venko9669-crypto/table/chain_link.png

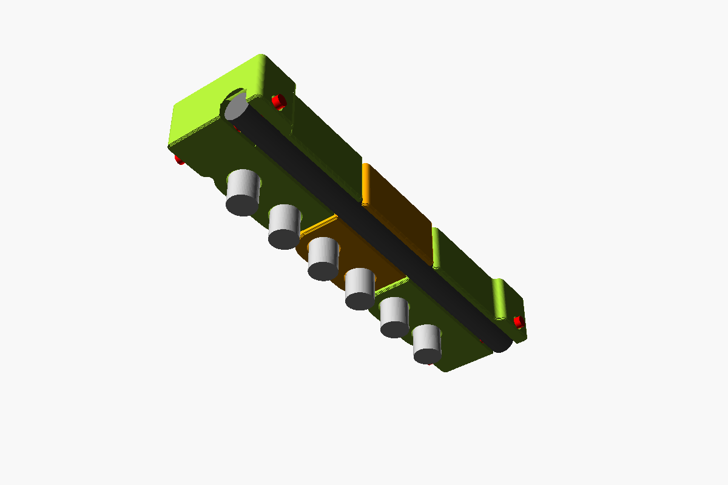
chain_link.png
