venko9669-crypto/table/chain_link_open.png

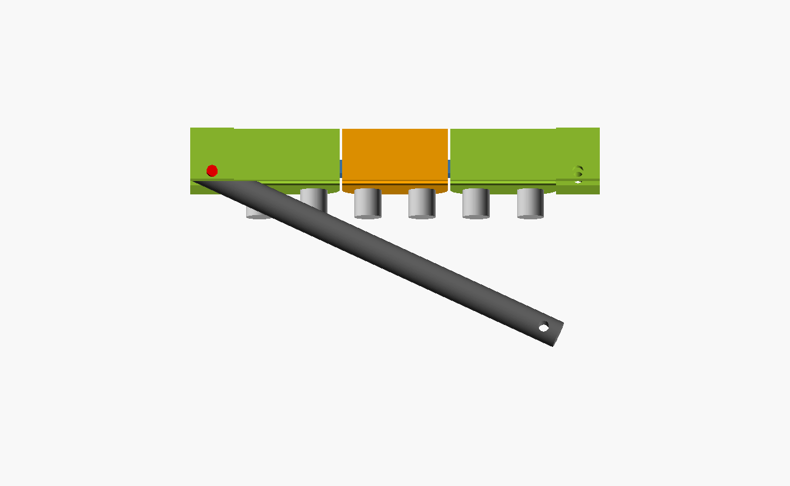
chain_link_open.png
