venko9669-crypto/table/creality/plates_preview.png

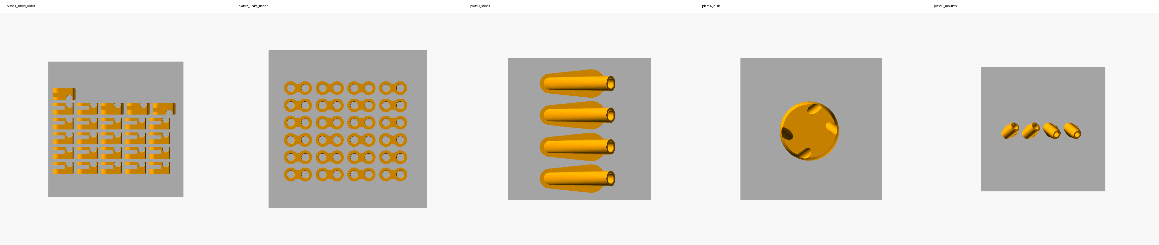
creality/plates_preview.png
