venko9669-crypto/table/folded_cutaway.png

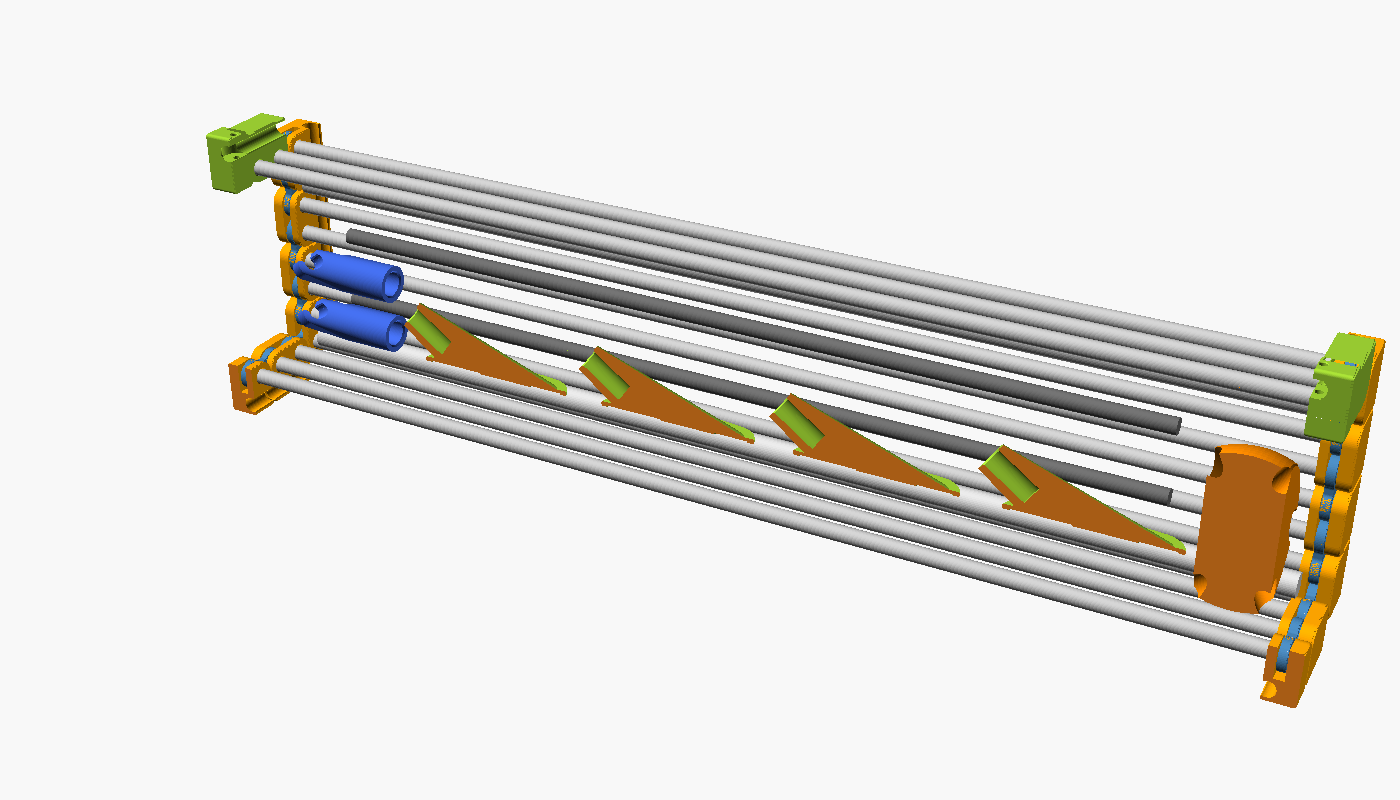
folded_cutaway.png
