venko9669-crypto/table/legs_hub.png

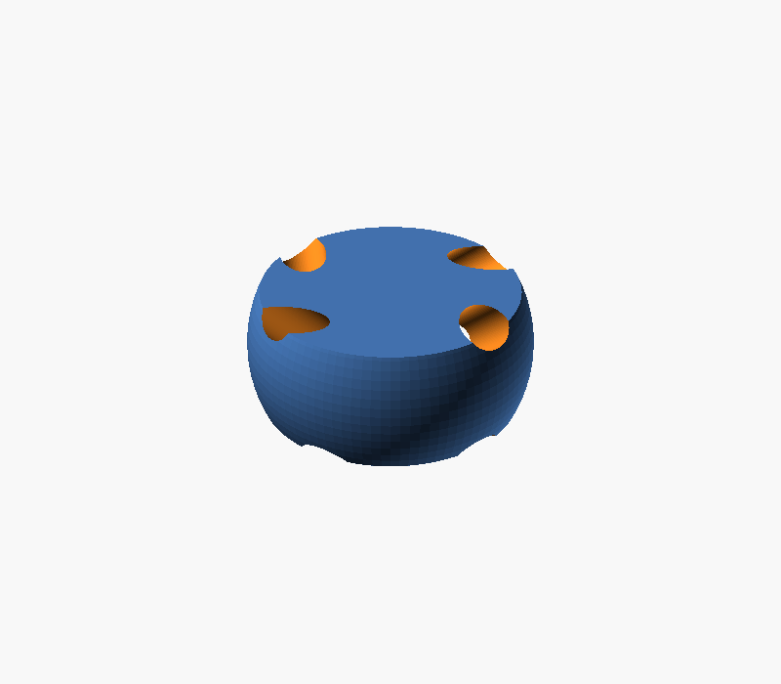
legs_hub.png
