venko9669-crypto/table/legs_mount.png

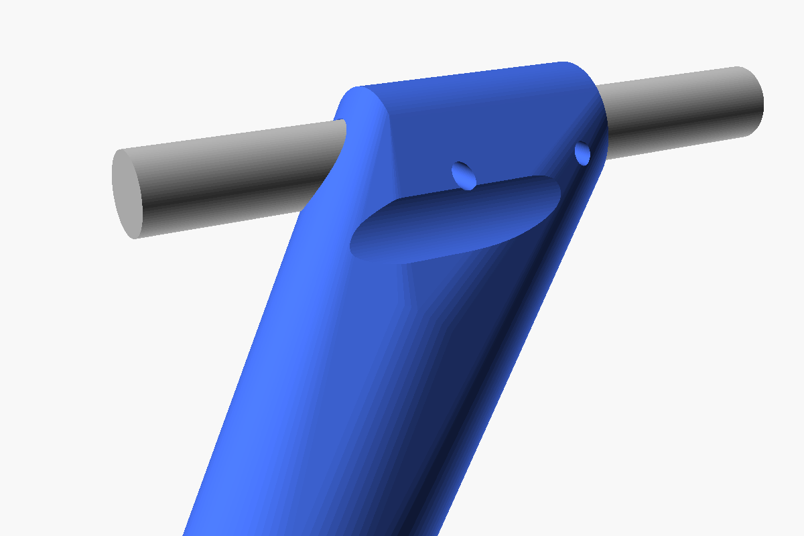
legs_mount.png
