venko9669-crypto/table/rolled.png

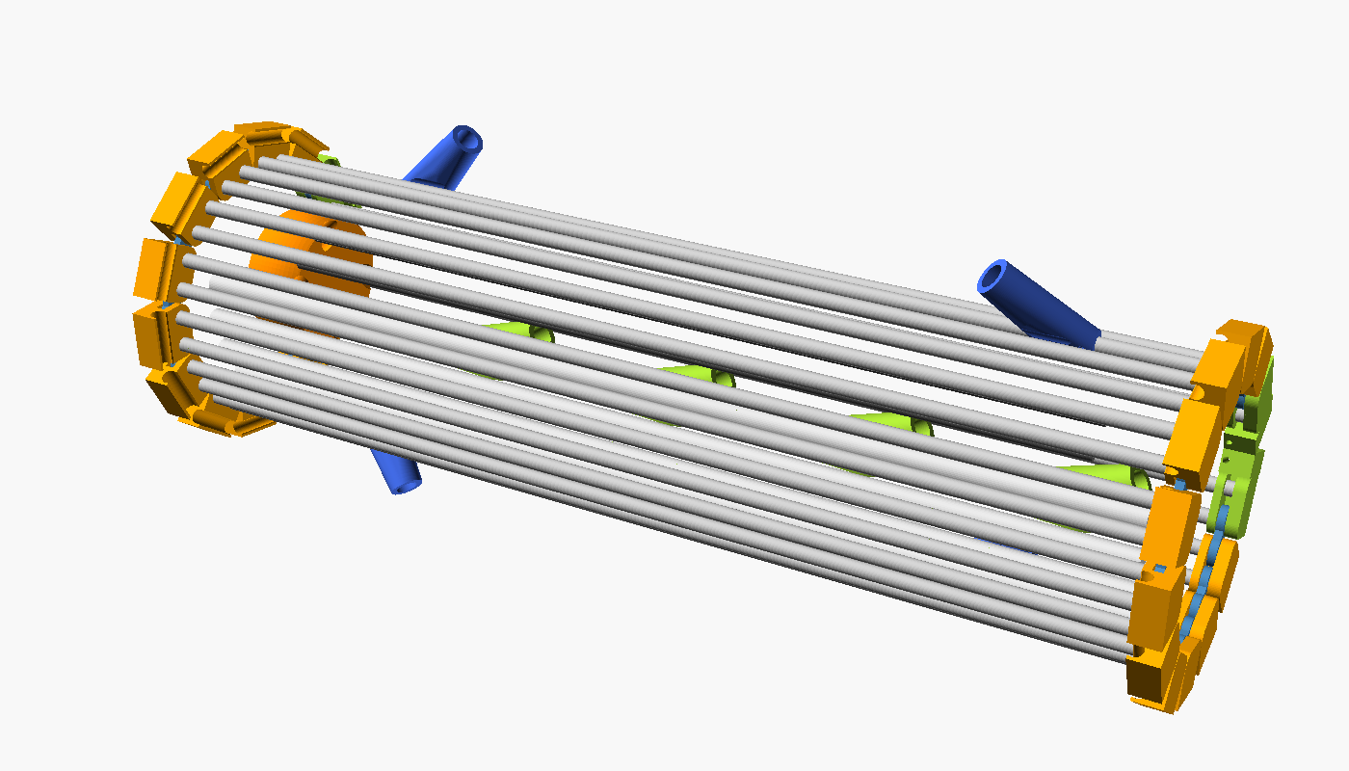
rolled.png
