venko9669-crypto/table/rolled_end.png

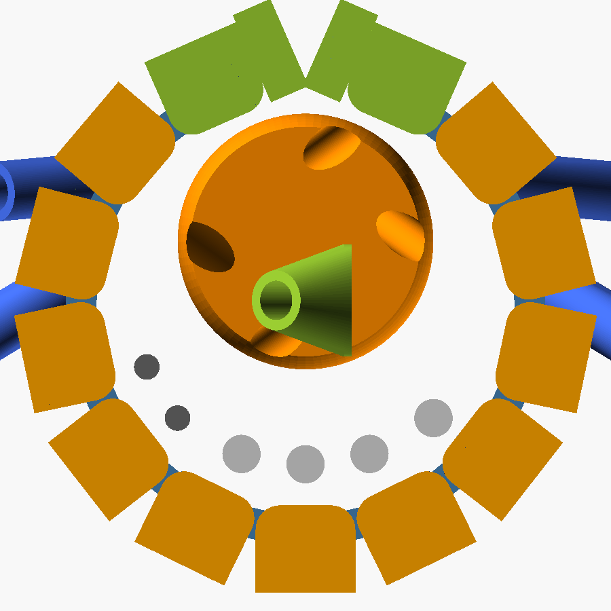
rolled_end.png
