venko9669-crypto/table/stl/all_parts.png

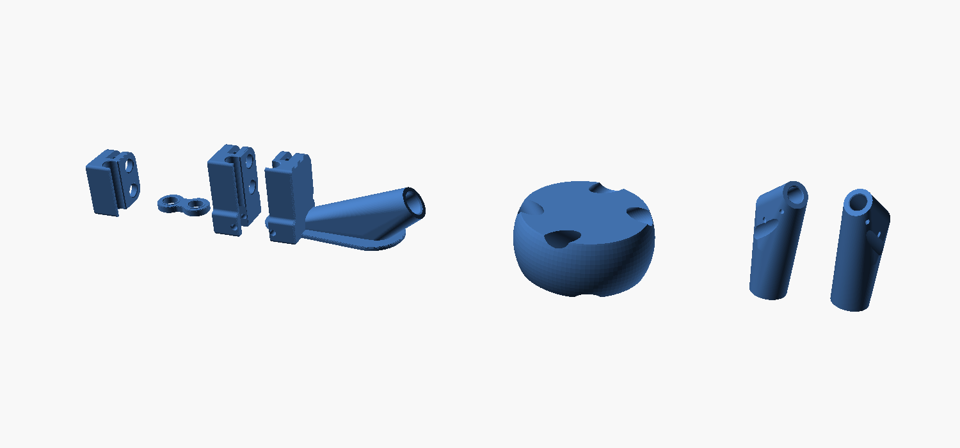
stl/all_parts.png
