venko9669-crypto/table/print_links.png

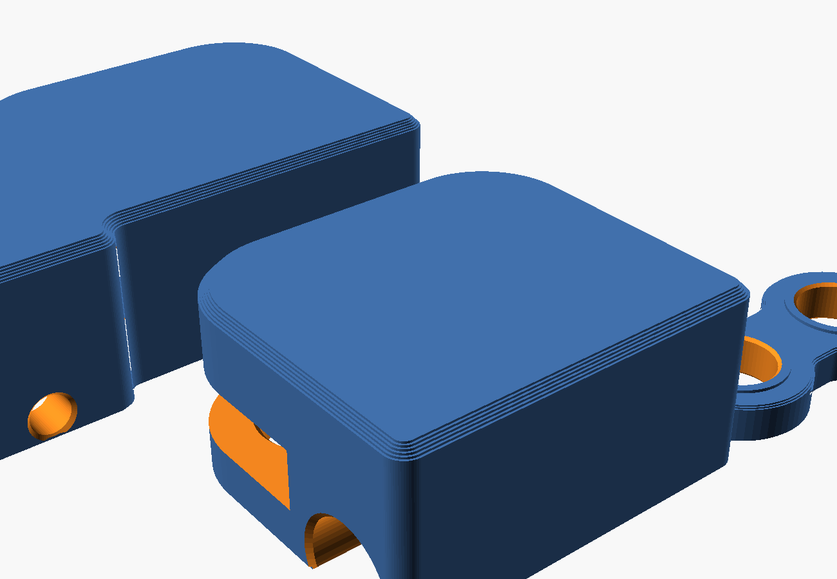
print_links.png
